im-redactd/saintcon2023_minibadge/src/timber_wheel.h

#ifndef TIMBER_WHEEL_H
#define TIMBER_WHEEL_H
/*
Generated from the following:
----
return [
  Math.cos(((position.x + position.y) * 1) + (time * tau)) * 0.5 + 0.5,
  0,
  Math.cos(((position.z + position.y) * 0.5) + (time * tau)) * 0.5 + 0.5
]
*/

static const uint32_t timber_wheel_led_count = 72;
static const uint32_t timber_wheel_frame_size = 216;
static const uint32_t timber_wheel_frame_count = 48;
static const uint32_t timber_wheel_frame_rate = 24;

static const PROGMEM uint8_t timber_wheel[] = {
		// frame index 0
	0xDE, 0x00, 0xF8, // 0
	0xEC, 0x00, 0xF8, // 1
	0xF6, 0x00, 0xF8, // 2
	0xFD, 0x00, 0xF8, // 3
	0xFF, 0x00, 0xF8, // 4
	0xFD, 0x00, 0xF8, // 5
	0xF6, 0x00, 0xF8, // 6
	0xEC, 0x00, 0xF8, // 7
	0xDE, 0x00, 0xF8, // 8
	0xDE, 0x00, 0xFC, // 9
	0xEC, 0x00, 0xFC, // 10
	0xF6, 0x00, 0xFC, // 11
	0xFD, 0x00, 0xFC, // 12
	0xFF, 0x00, 0xFC, // 13
	0xFD, 0x00, 0xFC, // 14
	0xF6, 0x00, 0xFC, // 15
	0xEC, 0x00, 0xFC, // 16
	0xDE, 0x00, 0xFC, // 17
	0xDE, 0x00, 0xFE, // 18
	0xEC, 0x00, 0xFE, // 19
	0xF6, 0x00, 0xFE, // 20
	0xFD, 0x00, 0xFE, // 21
	0xFF, 0x00, 0xFE, // 22
	0xFD, 0x00, 0xFE, // 23
	0xF6, 0x00, 0xFE, // 24
	0xEC, 0x00, 0xFE, // 25
	0xDE, 0x00, 0xFE, // 26
	0xDE, 0x00, 0xFF, // 27
	0xEC, 0x00, 0xFF, // 28
	0xF6, 0x00, 0xFF, // 29
	0xFD, 0x00, 0xFF, // 30
	0xFF, 0x00, 0xFF, // 31
	0xFD, 0x00, 0xFF, // 32
	0xF6, 0x00, 0xFF, // 33
	0xEC, 0x00, 0xFF, // 34
	0xDE, 0x00, 0xFF, // 35
	0xDE, 0x00, 0xFF, // 36
	0xEC, 0x00, 0xFF, // 37
	0xF6, 0x00, 0xFF, // 38
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
	0xF9, 0x00, 0xFF, // 30
	0xFE, 0x00, 0xFF, // 31
	0xFF, 0x00, 0xFF, // 32
	0xFB, 0x00, 0xFF, // 33
	0xF4, 0x00, 0xFF, // 34
	0xE8, 0x00, 0xFF, // 35
	0xE8, 0x00, 0xFD, // 36
	0xF4, 0x00, 0xFD, // 37
	0xFB, 0x00, 0xFD, // 38
	0xFF, 0x00, 0xFD, // 39
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
};

#endif /* TIMBER_WHEEL_H */
