im-redactd/saintcon2023_minibadge/src/ElectricBranches.h

#ifndef ELECTRICBRANCHES_H
#define ELECTRICBRANCHES_H

static const uint32_t ElectricBranches_led_count = 156;
static const uint32_t ElectricBranches_frame_size = 468;
static const uint32_t ElectricBranches_frame_count = 24;
static const uint32_t ElectricBranches_frame_rate = 24;

static const PROGMEM uint8_t ElectricBranches[] = {
	// frame index 0
	0xB8, 0xA9, 0xCC, // 0
	0xFF, 0xFF, 0xFF, // 1
	0xCD, 0xB9, 0xCD, // 2
	0x2B, 0x09, 0x51, // 3
	0x50, 0x2C, 0x6E, // 4
	0x55, 0x40, 0x7C, // 5
	0x9C, 0x41, 0xAF, // 6
	0xFF, 0xCB, 0xFF, // 7
	0xCD, 0x98, 0xE6, // 8
	0x3A, 0x45, 0xB3, // 9
	0xB4, 0xBC, 0xE0, // 10
	0xFF, 0xF2, 0xF5, // 11
	0x73, 0x7E, 0xD0, // 12
	0xC0, 0xE9, 0xFF, // 13
	0xAA, 0xA2, 0xBE, // 14
	0xC5, 0x91, 0xA9, // 15
	0x6C, 0x2C, 0x69, // 16
	0xCB, 0x86, 0x9D, // 17
	0xCD, 0x9A, 0xB0, // 18
	0x3D, 0x12, 0x75, // 19
	0xD3, 0x98, 0xCF, // 20
	0xFB, 0xF0, 0xFD, // 21
	0xF6, 0xF3, 0xFF, // 22
	0xCE, 0xC3, 0xE9, // 23
	0x4C, 0x51, 0xB6, // 24
	0x4D, 0x84, 0xD4, // 25
	0x72, 0x52, 0x86, // 26
	0x5C, 0x30, 0x70, // 27
	0x64, 0x20, 0x64, // 28
	0xA7, 0x50, 0x88, // 29
	0xF5, 0xB8, 0xBE, // 30
	0xAE, 0x73, 0x9B, // 31
	0x2B, 0x1D, 0x7B, // 32
	0xAF, 0xB2, 0xD6, // 33
	0xFF, 0xFF, 0xFF, // 34
	0xF6, 0xC7, 0xF1, // 35
	0x9C, 0x5B, 0xCC, // 36
	0x7F, 0x95, 0xE2, // 37
	0x48, 0x97, 0xDC, // 38
	0x4C, 0x00, 0x41, // 39
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

	// frame index 1
	0x95, 0x75, 0xA5, // 0
	0xFF, 0xFF, 0xFF, // 1
	0xE4, 0xD0, 0xDF, // 2
	0x42, 0x19, 0x5E, // 3
	0x3E, 0x24, 0x6C, // 4
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
	0xF6, 0xBA, 0xC0, // 30
	0xAE, 0x6E, 0x9A, // 31
	0x36, 0x2E, 0x89, // 32
	0xC4, 0xD7, 0xEC, // 33
	0xFF, 0xFF, 0xFF, // 34
	0xDD, 0xAC, 0xE3, // 35
	0x95, 0x53, 0xCA, // 36
	0x8F, 0x7A, 0xDD, // 37
	0x3B, 0x66, 0xCB, // 38
	0x4C, 0x06, 0x46, // 39
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
};

#endif /* ELECTRICBRANCHES_H */
