im-redactd/saintcon2023_minibadge/src/Fireworks.h

#ifndef FIREWORKS_H
#define FIREWORKS_H

static const uint32_t Fireworks_led_count = 104;
static const uint32_t Fireworks_frame_size = 312;
static const uint32_t Fireworks_frame_count = 29.25;
static const uint32_t Fireworks_frame_rate = 24;

static const uint8_t Fireworks[] = {
	// frame index 0
	0x00, 0x00, 0x00, // 0
	0x00, 0x00, 0x00, // 1
	0x00, 0x00, 0x00, // 2
	0x00, 0x00, 0x00, // 3
	0x00, 0x00, 0x00, // 4
	0x00, 0x00, 0x00, // 5
	0x00, 0x00, 0x00, // 6
	0x00, 0x00, 0x00, // 7
	0x00, 0x00, 0x00, // 8
	0x00, 0x00, 0x00, // 9
	0x00, 0x00, 0x00, // 10
	0x00, 0x00, 0x00, // 11
	0x00, 0x00, 0x00, // 12
	0x00, 0x00, 0x00, // 13
	0x00, 0x00, 0x00, // 14
	0x00, 0x00, 0x00, // 15
	0x00, 0x00, 0x00, // 16
	0x00, 0x00, 0x00, // 17
	0x00, 0x00, 0x00, // 18
	0x00, 0x00, 0x00, // 19
	0x00, 0x00, 0x00, // 20
	0x00, 0x00, 0x00, // 21
	0x00, 0x00, 0x00, // 22
	0x00, 0x00, 0x00, // 23
	0x00, 0x00, 0x00, // 24
	0x00, 0x00, 0x00, // 25
	0x00, 0x00, 0x00, // 26
	0x00, 0x00, 0x00, // 27
	0x00, 0x00, 0x00, // 28
	0x00, 0x00, 0x00, // 29
	0x00, 0x00, 0x00, // 30
	0x00, 0x00, 0x00, // 31
	0x00, 0x00, 0x00, // 32
	0x00, 0x00, 0x00, // 33
	0x00, 0x00, 0x00, // 34
	0x00, 0x00, 0x00, // 35
	0x00, 0x00, 0x00, // 36
	0x00, 0x00, 0x00, // 37
	0x00, 0x00, 0x00, // 38
	0x00, 0x00, 0x00, // 39
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

	// frame index 1
	0x00, 0x00, 0x00, // 0
	0x00, 0x00, 0x00, // 1
	0x00, 0x00, 0x00, // 2
	0x00, 0x00, 0x00, // 3
	0x00, 0x00, 0x00, // 4
	0x00, 0x00, 0x00, // 5
	0x00, 0x00, 0x00, // 6
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
	0x00, 0x00, 0x00, // 16
	0x00, 0x00, 0x00, // 17
	0x00, 0x00, 0x00, // 18
	0x2A, 0x36, 0x82, // 19
	0x00, 0x00, 0x00, // 20
	0x00, 0x00, 0x00, // 21
	0x00, 0x00, 0x00, // 22
	0x00, 0x00, 0x00, // 23
	0x00, 0x00, 0x00, // 24
	0x00, 0x00, 0x00 // 25
};

#endif /* FIREWORKS_H */
