im-redactd/saintcon2023_minibadge/src/Ghost.h

#ifndef GHOST_H
#define GHOST_H

static const uint32_t Ghost_led_count = 156;
static const uint32_t Ghost_frame_size = 468;
static const uint32_t Ghost_frame_count = 8;
static const uint32_t Ghost_frame_rate = 2;

static const PROGMEM uint8_t Ghost[] = {
	// frame index 0
	0x34, 0x34, 0x34, // 0
	0x34, 0x34, 0x34, // 1
	0x34, 0x34, 0x34, // 2
	0x00, 0x00, 0x00, // 3
	0x00, 0x00, 0x00, // 4
	0x00, 0x00, 0x00, // 5
	0x00, 0x00, 0x00, // 6
	0x00, 0x00, 0x00, // 7
	0x00, 0x00, 0x00, // 8
	0x00, 0x00, 0x00, // 9
	0x34, 0x34, 0x34, // 10
	0x34, 0x34, 0x34, // 11
	0x34, 0x34, 0x34, // 12
	0x34, 0x34, 0x34, // 13
	0x34, 0x34, 0x34, // 14
	0x00, 0x00, 0x00, // 15
	0x00, 0x00, 0x00, // 16
	0x00, 0x00, 0x00, // 17
	0xA1, 0x44, 0x99, // 18
	0xA1, 0x44, 0x99, // 19
	0xA1, 0x44, 0x99, // 20
	0x00, 0x00, 0x00, // 21
	0x00, 0x00, 0x00, // 22
	0x00, 0x00, 0x00, // 23
	0x34, 0x34, 0x34, // 24
	0x34, 0x34, 0x34, // 25
	0x34, 0x34, 0x34, // 26
	0x00, 0x00, 0x00, // 27
	0x00, 0x00, 0x00, // 28
	0xA1, 0x44, 0x99, // 29
	0xA1, 0x44, 0x99, // 30
	0xA1, 0x44, 0x99, // 31
	0xA1, 0x44, 0x99, // 32
	0xA1, 0x44, 0x99, // 33
	0xA1, 0x44, 0x99, // 34
	0xA1, 0x44, 0x99, // 35
	0x00, 0x00, 0x00, // 36
	0x00, 0x00, 0x00, // 37
	0x34, 0x34, 0x34, // 38
	0x34, 0x34, 0x34, // 39
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

	// frame index 1
	0x34, 0x34, 0x34, // 0
	0x34, 0x34, 0x34, // 1
	0x34, 0x34, 0x34, // 2
	0x00, 0x00, 0x00, // 3
	0x00, 0x00, 0x00, // 4
	0x00, 0x00, 0x00, // 5
	0x00, 0x00, 0x00, // 6
	0x00, 0x00, 0x00, // 7
	0x00, 0x00, 0x00, // 8
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
	0xA1, 0x44, 0x99, // 30
	0xA1, 0x44, 0x99, // 31
	0xA1, 0x44, 0x99, // 32
	0xA1, 0x44, 0x99, // 33
	0xA1, 0x44, 0x99, // 34
	0xA1, 0x44, 0x99, // 35
	0x00, 0x00, 0x00, // 36
	0x00, 0x00, 0x00, // 37
	0x34, 0x34, 0x34, // 38
	0x34, 0x34, 0x34, // 39
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
};

#endif /* GHOST_H */
