im-redactd/saintcon2023_minibadge/src/Goots.h

#ifndef GOOTS_H
#define GOOTS_H

static const uint32_t Goots_led_count = 72;
static const uint32_t Goots_frame_size = 216;
static const uint32_t Goots_frame_count = 54;
static const uint32_t Goots_frame_rate = 24;

static const uint16_t Goots_frame_timing[] = {
	1000,
    80,
    80,
    150,
    80,
    350,
    80,
    1600,
    100,
    100,
    900,
    900,
    200,
    200,
    200,
    1400,
    50,
    50,
    50,
    50,
    50,
    50,
    50,
    50,
    50,
    50,
    50,
    1500,
    1500,
    150,
    150,
    150,
    150,
    150,
    150,
    150,
    150,
    150,
    150,
    150,
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
};

static const uint8_t Goots[] = {
	// frame index 0
	0x00, 0x00, 0x00, // 0
	0x00, 0x00, 0x00, // 1
	0x00, 0x00, 0x00, // 2
	0x00, 0x00, 0x00, // 3
	0x00, 0x00, 0x00, // 4
	0x00, 0x00, 0x00, // 5
	0x00, 0x00, 0x00, // 6
	0x00, 0x00, 0x00, // 7
	0x00, 0x00, 0x00, // 8
	0x00, 0x00, 0x00, // 9
	0x00, 0x00, 0x00, // 10
	0xFF, 0xFF, 0xFF, // 11
	0xFF, 0xFF, 0xFF, // 12
	0x00, 0x00, 0x00, // 13
	0x00, 0x00, 0x00, // 14
	0x00, 0x00, 0x00, // 15
	0x00, 0x00, 0x00, // 16
	0x00, 0x00, 0x00, // 17
	0x00, 0x00, 0x00, // 18
	0xFF, 0xA5, 0x1D, // 19
	0xFF, 0xFF, 0xFF, // 20
	0xFF, 0xFF, 0xFF, // 21
	0x00, 0x00, 0x00, // 22
	0x00, 0x00, 0x00, // 23
	0x00, 0x00, 0x00, // 24
	0x00, 0x00, 0x00, // 25
	0x00, 0x00, 0x00, // 26
	0x00, 0x00, 0x00, // 27
	0x00, 0x00, 0x00, // 28
	0x00, 0x00, 0x00, // 29
	0xFF, 0xFF, 0xFF, // 30
	0x00, 0x00, 0x00, // 31
	0x00, 0x00, 0x00, // 32
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
	0xFF, 0xFF, 0xFF, // 30
	0x00, 0x00, 0x00, // 31
	0x00, 0x00, 0x00, // 32
	0x00, 0x00, 0x00, // 33
	0x00, 0x00, 0x00, // 34
	0x00, 0x00, 0x00, // 35
	0x00, 0x00, 0x00, // 36
	0x00, 0x00, 0x00, // 37
	0x00, 0x00, 0x00, // 38
	0xFF, 0xFF, 0xFF, // 39
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
};

#endif /* GOOTS_H */
