im-redactd/saintcon2023_minibadge/src/Hamster.h

#ifndef HAMSTER_H
#define HAMSTER_H

static const uint32_t Hamster_led_count = 156;
static const uint32_t Hamster_frame_size = 468;
static const uint32_t Hamster_frame_count = 24;
static const uint32_t Hamster_frame_rate = 8;

static const uint8_t Hamster[] = {
	// frame index 0
	0x00, 0x00, 0x00, // 0
	0x56, 0x31, 0x11, // 1
	0x56, 0x31, 0x11, // 2
	0x00, 0x00, 0x00, // 3
	0x00, 0x00, 0x00, // 4
	0x00, 0x00, 0x00, // 5
	0x00, 0x00, 0x00, // 6
	0x00, 0x00, 0x00, // 7
	0x00, 0x00, 0x00, // 8
	0x56, 0x31, 0x11, // 9
	0x56, 0x31, 0x11, // 10
	0x56, 0x31, 0x11, // 11
	0x00, 0x00, 0x00, // 12
	0x56, 0x31, 0x11, // 13
	0xE9, 0x8E, 0x2D, // 14
	0xE9, 0x8E, 0x2D, // 15
	0x56, 0x31, 0x11, // 16
	0x00, 0x00, 0x00, // 17
	0x00, 0x00, 0x00, // 18
	0x00, 0x00, 0x00, // 19
	0x00, 0x00, 0x00, // 20
	0x56, 0x31, 0x11, // 21
	0xE9, 0x8E, 0x2D, // 22
	0xE9, 0x8E, 0x2D, // 23
	0xE9, 0x8E, 0x2D, // 24
	0x56, 0x31, 0x11, // 25
	0x56, 0x31, 0x11, // 26
	0xEC, 0xB3, 0xD2, // 27
	0xE9, 0x8E, 0x2D, // 28
	0x56, 0x31, 0x11, // 29
	0x56, 0x31, 0x11, // 30
	0x57, 0x31, 0x12, // 31
	0x55, 0x30, 0x11, // 32
	0x56, 0x31, 0x11, // 33
	0x56, 0x31, 0x11, // 34
	0xE9, 0x8E, 0x2D, // 35
	0xEC, 0xB3, 0xD2, // 36
	0xEC, 0xB3, 0xD2, // 37
	0x56, 0x31, 0x11, // 38
	0x56, 0x31, 0x12, // 39
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

	// frame index 1
	0x00, 0x00, 0x00, // 0
	0x56, 0x31, 0x11, // 1
	0x56, 0x31, 0x11, // 2
	0x00, 0x00, 0x00, // 3
	0x00, 0x00, 0x00, // 4
	0x00, 0x00, 0x00, // 5
	0x00, 0x00, 0x00, // 6
	0x00, 0x00, 0x00, // 7
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
	0x56, 0x31, 0x11, // 30
	0x57, 0x31, 0x12, // 31
	0x55, 0x30, 0x11, // 32
	0x56, 0x31, 0x11, // 33
	0x56, 0x31, 0x11, // 34
	0xE9, 0x8E, 0x2D, // 35
	0xEC, 0xB3, 0xD2, // 36
	0xEC, 0xB3, 0xD2, // 37
	0x56, 0x31, 0x11, // 38
	0x56, 0x31, 0x12, // 39
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
};

#endif /* HAMSTER_H */
