im-redactd/saintcon2023_minibadge/src/Heart.h

#ifndef HEART_H
#define HEART_H

static const uint32_t Heart_led_count = 156;
static const uint32_t Heart_frame_size = 468;
static const uint32_t Heart_frame_count = 24;
static const uint32_t Heart_frame_rate = 24;

static const PROGMEM uint8_t Heart[] = {
	// frame index 0
	0x00, 0x00, 0x00, // 0
	0x00, 0x00, 0x00, // 1
	0x00, 0x00, 0x00, // 2
	0x00, 0x01, 0x03, // 3
	0x00, 0x04, 0x0B, // 4
	0x00, 0x01, 0x03, // 5
	0x00, 0x01, 0x03, // 6
	0x00, 0x00, 0x00, // 7
	0x00, 0x00, 0x00, // 8
	0x00, 0x00, 0x00, // 9
	0x00, 0x00, 0x00, // 10
	0x00, 0x00, 0x00, // 11
	0x00, 0x00, 0x00, // 12
	0x00, 0x00, 0x00, // 13
	0x00, 0x00, 0x00, // 14
	0x00, 0x0E, 0x1F, // 15
	0x00, 0x36, 0x5F, // 16
	0x00, 0x45, 0x77, // 17
	0x00, 0x3E, 0x6B, // 18
	0x00, 0x1B, 0x33, // 19
	0x02, 0x00, 0x00, // 20
	0x02, 0x00, 0x00, // 21
	0x00, 0x00, 0x00, // 22
	0x00, 0x00, 0x00, // 23
	0x00, 0x00, 0x00, // 24
	0x00, 0x00, 0x00, // 25
	0x00, 0x00, 0x00, // 26
	0x00, 0x08, 0x16, // 27
	0x00, 0x43, 0x74, // 28
	0x00, 0x67, 0xAD, // 29
	0x00, 0x6F, 0xBA, // 30
	0x00, 0x6D, 0xB7, // 31
	0x15, 0x59, 0x96, // 32
	0x4A, 0x1D, 0x36, // 33
	0x43, 0x00, 0x01, // 34
	0x19, 0x00, 0x00, // 35
	0x00, 0x00, 0x00, // 36
	0x00, 0x00, 0x00, // 37
	0x00, 0x00, 0x00, // 38
	0x00, 0x00, 0x00, // 39
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

	// frame index 1
	0x00, 0x00, 0x00, // 0
	0x00, 0x00, 0x00, // 1
	0x00, 0x00, 0x00, // 2
	0x00, 0x01, 0x02, // 3
	0x00, 0x04, 0x0C, // 4
	0x00, 0x01, 0x03, // 5
	0x00, 0x01, 0x02, // 6
	0x00, 0x00, 0x00, // 7
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
	0x00, 0x6E, 0xB8, // 30
	0x00, 0x6C, 0xB4, // 31
	0x12, 0x58, 0x96, // 32
	0x49, 0x1E, 0x38, // 33
	0x46, 0x00, 0x01, // 34
	0x1C, 0x00, 0x00, // 35
	0x00, 0x00, 0x00, // 36
	0x00, 0x00, 0x00, // 37
	0x00, 0x00, 0x00, // 38
	0x00, 0x00, 0x00, // 39
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
};

#endif /* HEART_H */
