im-redactd/saintcon2023_minibadge/src/HexTubeAlt.h

#ifndef HEXTUBEALT_H
#define HEXTUBEALT_H

static const uint32_t HexTubeAlt_led_count = 156;
static const uint32_t HexTubeAlt_frame_size = 468;
static const uint32_t HexTubeAlt_frame_count = 24;
static const uint32_t HexTubeAlt_frame_rate = 24;

static const PROGMEM uint8_t HexTubeAlt[] = {
	// frame index 0
	0xD8, 0x95, 0x4F, // 0
	0xD0, 0x8E, 0x21, // 1
	0x88, 0x21, 0x0C, // 2
	0xA4, 0x76, 0x00, // 3
	0xAC, 0x81, 0x00, // 4
	0x0B, 0x01, 0x05, // 5
	0x2B, 0x1F, 0x02, // 6
	0xBC, 0x95, 0x11, // 7
	0x55, 0x3F, 0x0F, // 8
	0x00, 0x00, 0x09, // 9
	0x4E, 0x2B, 0x0B, // 10
	0xFB, 0xD3, 0x6E, // 11
	0xFF, 0xFF, 0xED, // 12
	0xED, 0xA9, 0x68, // 13
	0xF5, 0x8B, 0x3A, // 14
	0xFD, 0x9E, 0x19, // 15
	0xBB, 0x62, 0x28, // 16
	0x42, 0x21, 0x20, // 17
	0x0E, 0x07, 0x03, // 18
	0x20, 0x16, 0x00, // 19
	0x57, 0x39, 0x08, // 20
	0x30, 0x1B, 0x0B, // 21
	0x1E, 0x14, 0x06, // 22
	0x4B, 0x2E, 0x16, // 23
	0x94, 0x61, 0x25, // 24
	0xD5, 0x8B, 0x3D, // 25
	0xF0, 0xC1, 0x3D, // 26
	0xD6, 0x68, 0x25, // 27
	0xEB, 0x97, 0x18, // 28
	0x90, 0x3C, 0x37, // 29
	0x2C, 0x04, 0x17, // 30
	0x18, 0x1B, 0x00, // 31
	0x0C, 0x04, 0x0C, // 32
	0x2A, 0x06, 0x21, // 33
	0x39, 0x26, 0x11, // 34
	0x9C, 0x7D, 0x12, // 35
	0x66, 0x51, 0x16, // 36
	0x1E, 0x0C, 0x14, // 37
	0x88, 0x4F, 0x0B, // 38
	0xF0, 0x96, 0x3D, // 39
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

	// frame index 1
	0xDE, 0x9E, 0x49, // 0
	0xE4, 0x99, 0x1B, // 1
	0xAE, 0x44, 0x0E, // 2
	0xE0, 0xAB, 0x4F, // 3
	0xB4, 0x87, 0x33, // 4
	0x0A, 0x02, 0x04, // 5
	0x3A, 0x29, 0x01, // 6
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
	0x2A, 0x00, 0x21, // 30
	0x1E, 0x1D, 0x00, // 31
	0x0C, 0x08, 0x08, // 32
	0x22, 0x07, 0x16, // 33
	0x2E, 0x1C, 0x0D, // 34
	0x8D, 0x73, 0x16, // 35
	0x75, 0x60, 0x20, // 36
	0x27, 0x14, 0x13, // 37
	0x75, 0x42, 0x0C, // 38
	0xCE, 0x63, 0x30, // 39
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
};

#endif /* HEXTUBEALT_H */
