im-redactd/saintcon2023_minibadge/src/Honk.h

#ifndef HONK_H
#define HONK_H

static const uint32_t Honk_led_count = 156;
static const uint32_t Honk_frame_size = 468;
static const uint32_t Honk_frame_count = 6;
static const uint32_t Honk_frame_rate = 24;

static const uint16_t Honk_frame_timing[] = {
	1000,
	100,
	250,
	100,
	250,
	100
};

static const PROGMEM uint8_t Honk[] = {
	// frame index 0
	0x00, 0x00, 0x00, // 0
	0x00, 0x00, 0x00, // 1
	0x00, 0x00, 0x00, // 2
	0x00, 0x00, 0x00, // 3
	0x00, 0x00, 0x00, // 4
	0x00, 0x00, 0x00, // 5
	0x00, 0x00, 0x00, // 6
	0x00, 0x00, 0x00, // 7
	0x00, 0x00, 0x00, // 8
	0x00, 0x00, 0x00, // 9
	0x00, 0x00, 0x00, // 10
	0x00, 0x00, 0x00, // 11
	0x00, 0x00, 0x00, // 12
	0x00, 0x00, 0x00, // 13
	0x00, 0x00, 0x00, // 14
	0x00, 0x00, 0x00, // 15
	0x00, 0x00, 0x00, // 16
	0x00, 0x00, 0x00, // 17
	0x00, 0x00, 0x00, // 18
	0x59, 0x56, 0x52, // 19
	0x59, 0x56, 0x52, // 20
	0x59, 0x56, 0x52, // 21
	0x00, 0x00, 0x00, // 22
	0x00, 0x00, 0x00, // 23
	0x00, 0x00, 0x00, // 24
	0x00, 0x00, 0x00, // 25
	0x00, 0x00, 0x00, // 26
	0x00, 0x00, 0x00, // 27
	0x00, 0x00, 0x00, // 28
	0x00, 0x00, 0x00, // 29
	0x00, 0x00, 0x00, // 30
	0x59, 0x56, 0x52, // 31
	0xFF, 0xFF, 0xFF, // 32
	0xFF, 0xFF, 0xFF, // 33
	0xFF, 0xFF, 0xFF, // 34
	0x59, 0x56, 0x52, // 35
	0x00, 0x00, 0x00, // 36
	0x00, 0x00, 0x00, // 37
	0x00, 0x00, 0x00, // 38
	0x00, 0x00, 0x00, // 39
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

	// frame index 1
	0x00, 0x00, 0x00, // 0
	0x00, 0x00, 0x00, // 1
	0x00, 0x00, 0x00, // 2
	0x00, 0x00, 0x00, // 3
	0x66, 0x39, 0x31, // 4
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
	0x00, 0x00, 0x00, // 30
	0x59, 0x56, 0x52, // 31
	0xFF, 0xFF, 0xFF, // 32
	0xFF, 0xFF, 0xFF, // 33
	0xFF, 0xFF, 0xFF, // 34
	0xFF, 0xFF, 0xFF, // 35
	0x59, 0x56, 0x52, // 36
	0x00, 0x00, 0x00, // 37
	0x00, 0x00, 0x00, // 38
	0x00, 0x00, 0x00, // 39
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
};

#endif /* HONK_H */
