im-redactd/saintcon2023_minibadge/src/IntersectingCircles.h

#ifndef INTERSECTINGCIRCLES_H
#define INTERSECTINGCIRCLES_H
/*
Generated from the following:
----
const angle = Math.atan2(position.z, position.x);
const distance = Math.sqrt(Math.pow(position.x,2) + Math.pow(position.z,2));
const offset = (distance + time) * tau;
return [
  (Math.cos((position.x + time) * tau) + Math.sin((-position.z + time) * tau)) * 1 - 0.5,
  (Math.cos((-position.x + time) * tau) + Math.sin((position.z + time) * tau)) * 1 - 0.5,
  (Math.cos((position.z + time) * tau) + Math.sin((position.x + time) * tau)) * 1 - 0.5,
]
*/

static const uint32_t IntersectingCircles_led_count = 72;
static const uint32_t IntersectingCircles_frame_size = 216;
static const uint32_t IntersectingCircles_frame_count = 48;
static const uint32_t IntersectingCircles_frame_rate = 24;

static const PROGMEM uint8_t IntersectingCircles[] = {
	// frame index 0
	0x40, 0x00, 0x00, // 0
	0x00, 0x00, 0x00, // 1
	0x00, 0x00, 0x00, // 2
	0xB2, 0x00, 0x00, // 3
	0xFF, 0x00, 0x00, // 4
	0xB2, 0x00, 0x00, // 5
	0x00, 0x00, 0x00, // 6
	0x00, 0x00, 0x00, // 7
	0x40, 0x00, 0x00, // 8
	0x00, 0x00, 0x00, // 9
	0x00, 0x00, 0x00, // 10
	0x00, 0x00, 0x00, // 11
	0x00, 0x1F, 0x00, // 12
	0x45, 0xBA, 0x00, // 13
	0x00, 0x1F, 0x00, // 14
	0x00, 0x00, 0x00, // 15
	0x00, 0x00, 0x00, // 16
	0x00, 0x00, 0x00, // 17
	0x00, 0x6E, 0x00, // 18
	0x00, 0x00, 0x00, // 19
	0x00, 0x00, 0x0D, // 20
	0x00, 0xE0, 0x3E, // 21
	0x00, 0xFF, 0x00, // 22
	0x00, 0xE0, 0x00, // 23
	0x00, 0x00, 0x00, // 24
	0x00, 0x00, 0x00, // 25
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
	0x00, 0x72, 0x00, // 30
	0x00, 0xED, 0x45, // 31
	0x00, 0x35, 0xFF, // 32
	0x00, 0x00, 0xFF, // 33
	0x00, 0x00, 0x2E, // 34
	0x00, 0x03, 0x00, // 35
	0x00, 0x00, 0x00, // 36
	0x00, 0x00, 0x09, // 37
	0x00, 0x00, 0xFF, // 38
	0x72, 0x00, 0xFF, // 39
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
};

#endif /* INTERSECTINGCIRCLES_H */
