im-redactd/saintcon2023_minibadge/src/MagicSpellOrb.h

#ifndef MAGICSPELLORB_H
#define MAGICSPELLORB_H

static const uint32_t MagicSpellOrb_led_count = 156;
static const uint32_t MagicSpellOrb_frame_size = 468;
static const uint32_t MagicSpellOrb_frame_count = 48;
static const uint32_t MagicSpellOrb_frame_rate = 24;

static const PROGMEM uint8_t MagicSpellOrb[] = {
	// frame index 0
	0x0D, 0x0D, 0x00, // 0
	0x17, 0x12, 0x00, // 1
	0x27, 0x05, 0x00, // 2
	0x07, 0x00, 0x00, // 3
	0x00, 0x00, 0x0C, // 4
	0x32, 0x0C, 0x60, // 5
	0x54, 0x03, 0x45, // 6
	0x08, 0x00, 0x00, // 7
	0x00, 0x03, 0x00, // 8
	0x1B, 0x08, 0x22, // 9
	0x2A, 0x0C, 0x45, // 10
	0x1E, 0x2F, 0x37, // 11
	0x00, 0x56, 0x2A, // 12
	0x3B, 0x14, 0x3C, // 13
	0x7A, 0x3E, 0x4D, // 14
	0x94, 0x6A, 0x3E, // 15
	0x8B, 0x80, 0x46, // 16
	0x6A, 0x4D, 0x19, // 17
	0x19, 0x14, 0x00, // 18
	0x20, 0x00, 0x0C, // 19
	0x80, 0x00, 0x68, // 20
	0x8D, 0x00, 0x85, // 21
	0x4B, 0x16, 0x41, // 22
	0x2F, 0x31, 0x32, // 23
	0x51, 0x32, 0x74, // 24
	0x74, 0x52, 0x8D, // 25
	0xCD, 0x34, 0x9C, // 26
	0xB5, 0x05, 0xD3, // 27
	0x75, 0x20, 0xCB, // 28
	0x65, 0xA3, 0xD2, // 29
	0x7C, 0xF8, 0xA3, // 30
	0x34, 0xFF, 0x6F, // 31
	0x68, 0x3C, 0x9E, // 32
	0xF5, 0x00, 0xC8, // 33
	0xA9, 0x12, 0x9E, // 34
	0xC3, 0x07, 0xC3, // 35
	0x92, 0x63, 0x60, // 36
	0x56, 0xA1, 0x17, // 37
	0x37, 0x81, 0x7A, // 38
	0x5C, 0x46, 0x00, // 39
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

	// frame index 1
	0x0C, 0x00, 0x00, // 0
	0x1B, 0x00, 0x00, // 1
	0x23, 0x00, 0x0C, // 2
	0x16, 0x00, 0x07, // 3
	0x00, 0x00, 0x05, // 4
	0x0A, 0x00, 0x39, // 5
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
	0x6B, 0xC3, 0xB9, // 30
	0x00, 0xFF, 0xBA, // 31
	0x79, 0x43, 0x81, // 32
	0xFF, 0x00, 0x6D, // 33
	0xC9, 0x2C, 0xAE, // 34
	0xFF, 0x14, 0xD3, // 35
	0x72, 0x51, 0x90, // 36
	0x2A, 0xA3, 0x52, // 37
	0x51, 0x8B, 0xA6, // 38
	0x77, 0x7C, 0x00, // 39
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
};

#endif /* MAGICSPELLORB_H */
