im-redactd/saintcon2023_minibadge/src/RainbowSlinky.h

#ifndef RAINBOWSLINKY_H
#define RAINBOWSLINKY_H

static const uint32_t RainbowSlinky_led_count = 156;
static const uint32_t RainbowSlinky_frame_size = 468;
static const uint32_t RainbowSlinky_frame_count = 24;
static const uint32_t RainbowSlinky_frame_rate = 24;

static const PROGMEM uint8_t RainbowSlinky[] = {
	// frame index 0
	0x00, 0x83, 0x51, // 0
	0x00, 0x63, 0x3E, // 1
	0x00, 0x39, 0x3E, // 2
	0x00, 0x6F, 0x51, // 3
	0x00, 0x35, 0x34, // 4
	0x00, 0x49, 0x54, // 5
	0x00, 0x55, 0x4E, // 6
	0x00, 0x1C, 0x27, // 7
	0x00, 0x41, 0x53, // 8
	0x00, 0x3B, 0x42, // 9
	0x00, 0x14, 0x27, // 10
	0x06, 0x33, 0x4E, // 11
	0x07, 0x24, 0x32, // 12
	0x00, 0x66, 0x54, // 13
	0x00, 0x9F, 0x5A, // 14
	0x00, 0x42, 0x3A, // 15
	0x00, 0x78, 0x62, // 16
	0x00, 0x66, 0x4E, // 17
	0x00, 0x30, 0x46, // 18
	0x00, 0x73, 0x6C, // 19
	0x00, 0x40, 0x3E, // 20
	0x00, 0x2A, 0x47, // 21
	0x00, 0x55, 0x62, // 22
	0x00, 0x26, 0x2F, // 23
	0x04, 0x2A, 0x4B, // 24
	0x0A, 0x39, 0x52, // 25
	0x00, 0x6A, 0x51, // 26
	0x00, 0xC6, 0x76, // 27
	0x00, 0x89, 0x55, // 28
	0x00, 0x58, 0x5B, // 29
	0x00, 0x9D, 0x72, // 30
	0x00, 0x43, 0x45, // 31
	0x00, 0x6E, 0x7B, // 32
	0x00, 0x74, 0x6A, // 33
	0x00, 0x21, 0x34, // 34
	0x00, 0x5F, 0x78, // 35
	0x00, 0x4E, 0x58, // 36
	0x00, 0x1A, 0x37, // 37
	0x0A, 0x47, 0x6E, // 38
	0x00, 0x99, 0x57, // 39
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

	// frame index 1
	0x00, 0x79, 0x51, // 0
	0x00, 0x6C, 0x42, // 1
	0x00, 0x34, 0x3A, // 2
	0x00, 0x6F, 0x53, // 3
	0x00, 0x3C, 0x36, // 4
	0x00, 0x3F, 0x4E, // 5
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
	0x00, 0x99, 0x6E, // 30
	0x00, 0x3C, 0x45, // 31
	0x00, 0x7B, 0x80, // 32
	0x00, 0x6C, 0x63, // 33
	0x00, 0x20, 0x38, // 34
	0x00, 0x65, 0x7A, // 35
	0x00, 0x47, 0x4F, // 36
	0x00, 0x1E, 0x3F, // 37
	0x0A, 0x49, 0x6D, // 38
	0x00, 0x8C, 0x55, // 39
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
};

#endif /* RAINBOWSLINKY_H */
