im-redactd/saintcon2023_minibadge/src/RainbowTorusSpirals.h

#ifndef RAINBOWTORUSSPIRALS_H
#define RAINBOWTORUSSPIRALS_H

static const uint32_t RainbowTorusSpirals_led_count = 72;
static const uint32_t RainbowTorusSpirals_frame_size = 216;
static const uint32_t RainbowTorusSpirals_frame_count = 48;
static const uint32_t RainbowTorusSpirals_frame_rate = 24;

static const uint8_t RainbowTorusSpirals[] = {
	// frame index 0
	0x00, 0x00, 0x01, // 0
	0x00, 0x00, 0x01, // 1
	0x2C, 0x00, 0x03, // 2
	0x57, 0x11, 0x00, // 3
	0x00, 0x00, 0x01, // 4
	0x00, 0x00, 0x01, // 5
	0x00, 0x00, 0x01, // 6
	0x00, 0x00, 0x01, // 7
	0x00, 0x00, 0x01, // 8
	0x00, 0x00, 0x01, // 9
	0x00, 0x00, 0x01, // 10
	0xC0, 0x18, 0x0E, // 11
	0xE1, 0x61, 0x00, // 12
	0xB7, 0x74, 0x00, // 13
	0x1A, 0x10, 0x00, // 14
	0x00, 0x00, 0x01, // 15
	0x00, 0x00, 0x01, // 16
	0x00, 0x00, 0x01, // 17
	0x00, 0x00, 0x01, // 18
	0x00, 0x00, 0x01, // 19
	0xC7, 0x04, 0x44, // 20
	0xDF, 0x35, 0x04, // 21
	0xE1, 0x61, 0x00, // 22
	0xC7, 0xAF, 0x00, // 23
	0x8F, 0x95, 0x02, // 24
	0x01, 0x12, 0x00, // 25
	0x00, 0x00, 0x01, // 26
	0x00, 0x00, 0x01, // 27
	0x00, 0x00, 0x01, // 28
	0xD3, 0x00, 0x7B, // 29
	0xDA, 0x16, 0x26, // 30
	0x9F, 0x46, 0x19, // 31
	0x60, 0xCD, 0x08, // 32
	0x97, 0xDC, 0x00, // 33
	0x60, 0xCD, 0x08, // 34
	0x00, 0x00, 0x01, // 35
	0x00, 0x00, 0x01, // 36
	0x00, 0x00, 0x01, // 37
	0x5D, 0x00, 0xBE, // 38
	0x26, 0x12, 0xCA, // 39
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

	// frame index 1
	0x00, 0x00, 0x01, // 0
	0x00, 0x00, 0x01, // 1
	0x2C, 0x00, 0x03, // 2
	0x3A, 0x00, 0x01, // 3
	0x00, 0x00, 0x01, // 4
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
	0xDA, 0x16, 0x26, // 30
	0x9F, 0x46, 0x19, // 31
	0x4D, 0xCA, 0x21, // 32
	0x6C, 0xDC, 0x00, // 33
	0x31, 0xC0, 0x18, // 34
	0x00, 0x00, 0x01, // 35
	0x00, 0x00, 0x01, // 36
	0x00, 0x00, 0x01, // 37
	0x73, 0x00, 0xBB, // 38
	0x45, 0x02, 0xC3, // 39
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
};

#endif /* RAINBOWTORUSSPIRALS_H */
