im-redactd/saintcon2023_minibadge/src/SlowRainbowSpiral.h

#ifndef SLOWRAINBOWSPIRAL_H
#define SLOWRAINBOWSPIRAL_H
/*
Generated from the following:
----
const angle = Math.atan2(position.z, position.x);
const distance = Math.sqrt(Math.pow(position.x,2) + Math.pow(position.z,2));
const offset = (distance + time) * tau;
return [
  Math.cos(offset + angle) * 0.5 + 0.5,
  Math.sin(offset + angle + pi) * 0.5 + 0.25,
  Math.sin(offset + angle) * 0.5 + 0.5,
]
*/

static const uint32_t SlowRainbowSpiral_led_count = 72;
static const uint32_t SlowRainbowSpiral_frame_size = 216;
static const uint32_t SlowRainbowSpiral_frame_count = 48;
static const uint32_t SlowRainbowSpiral_frame_rate = 12;

static const PROGMEM uint8_t SlowRainbowSpiral[] = {
	// frame index 0
	0xE7, 0x00, 0xCA, // 0
	0xFF, 0x46, 0x79, // 1
	0xED, 0x81, 0x3E, // 2
	0xDD, 0x97, 0x28, // 3
	0xE6, 0x8B, 0x34, // 4
	0xFD, 0x58, 0x67, // 5
	0xEF, 0x02, 0xBD, // 6
	0x9A, 0x00, 0xFC, // 7
	0x28, 0x00, 0xDC, // 8
	0x63, 0x00, 0xFC, // 9
	0xE0, 0x00, 0xD3, // 10
	0xF9, 0x67, 0x59, // 11
	0xAE, 0xB6, 0x09, // 12
	0x62, 0xBC, 0x03, // 13
	0x4F, 0xB6, 0x09, // 14
	0x74, 0xBF, 0x00, // 15
	0xC0, 0xAE, 0x12, // 16
	0xFC, 0x5D, 0x62, // 17
	0xCA, 0xA7, 0x18, // 18
	0x55, 0xB8, 0x07, // 19
	0x0B, 0x73, 0x4C, // 20
	0x00, 0x38, 0x87, // 21
	0x02, 0x56, 0x69, // 22
	0x48, 0xB2, 0x0D, // 23
	0xD1, 0xA1, 0x1E, // 24
	0xF9, 0x1A, 0xA5, // 25
	0x8C, 0x00, 0xFE, // 26
	0x92, 0x00, 0xFE, // 27
	0xFB, 0x22, 0x9D, // 28
	0xC6, 0xAA, 0x15, // 29
	0x2A, 0x9F, 0x21, // 30
	0x39, 0x00, 0xEA, // 31
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
	0x67, 0x00, 0xFD, // 29
	0xF3, 0x09, 0xB6, // 30
	0x98, 0xBD, 0x02, // 31
	0x66, 0xBD, 0x02, // 32
	0xD0, 0xA3, 0x1D, // 33
	0xFD, 0x2A, 0x95, // 34
	0xA3, 0x00, 0xFA, // 35
	0xC0, 0x00, 0xED, // 36
	0xFD, 0x54, 0x6C, // 37
	0x98, 0xBD, 0x02, // 38
	0x0C, 0x77, 0x49, // 39
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
